ttankbuster/CyberwatchV1B/docs/images/cyan-loading.png

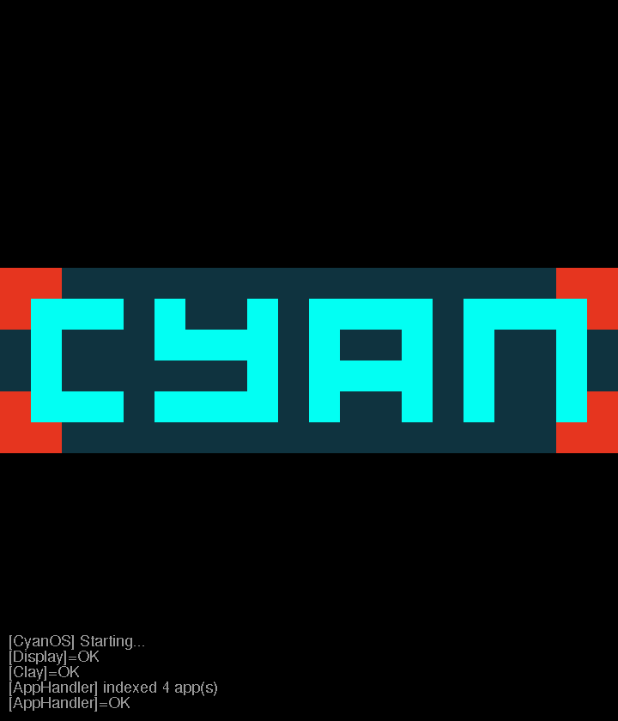
docs/images/cyan-loading.png
