ttankbuster/CyberwatchV1B/docs/images/dial-design-2.png

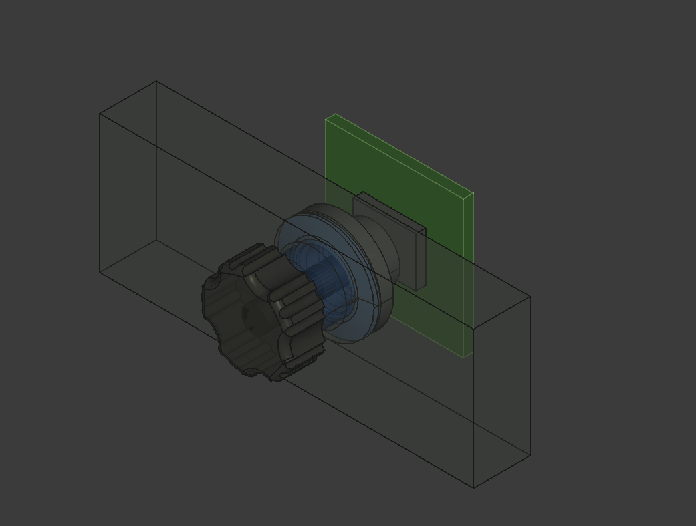
docs/images/dial-design-2.png
