ttankbuster/CyberwatchV1B/docs/images/pcb-3d-2.png

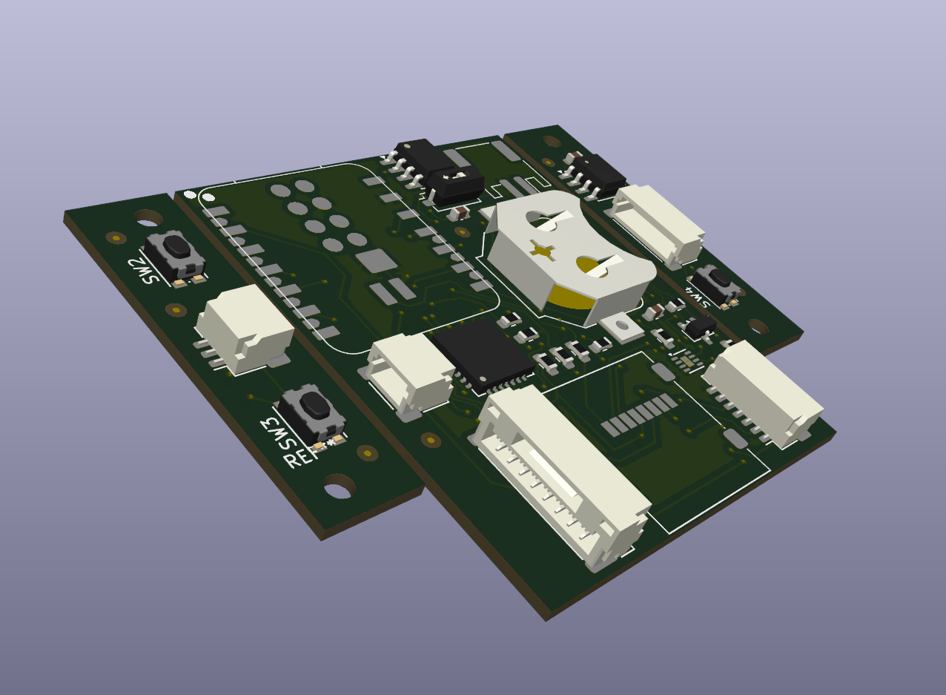
docs/images/pcb-3d-2.png
