ttankbuster/CyberwatchV1B/docs/images/pcb-3d-3.png

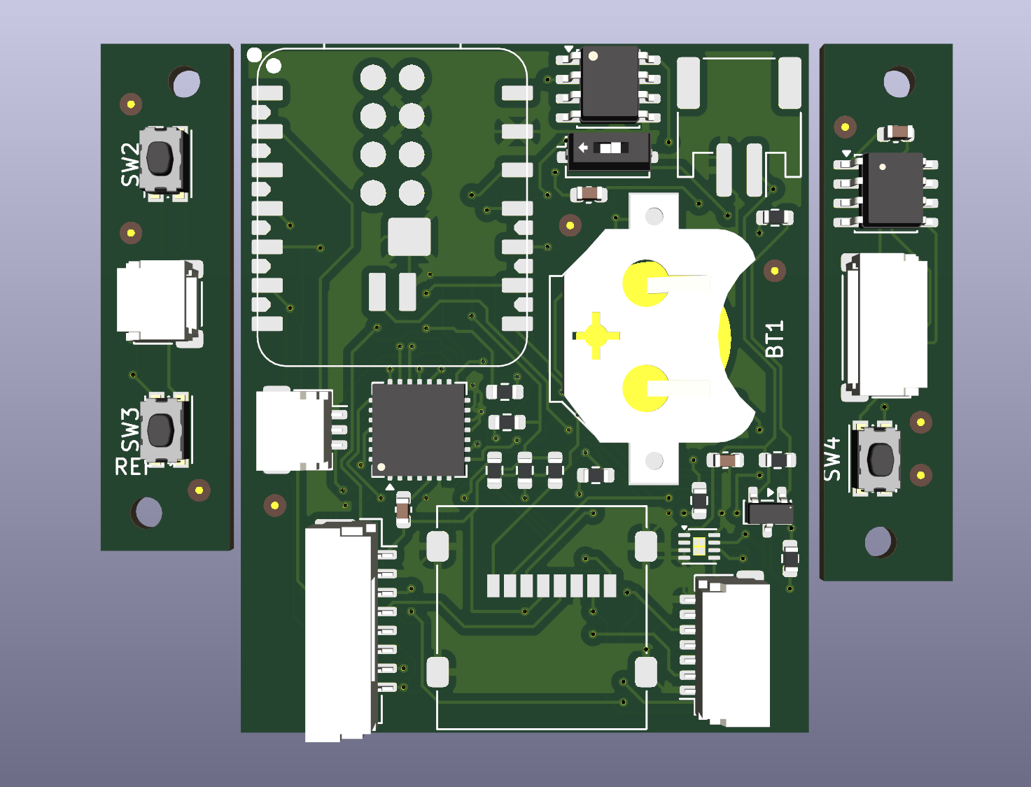
docs/images/pcb-3d-3.png
