ttankbuster/CyberwatchV1B/docs/images/pcb-design.png

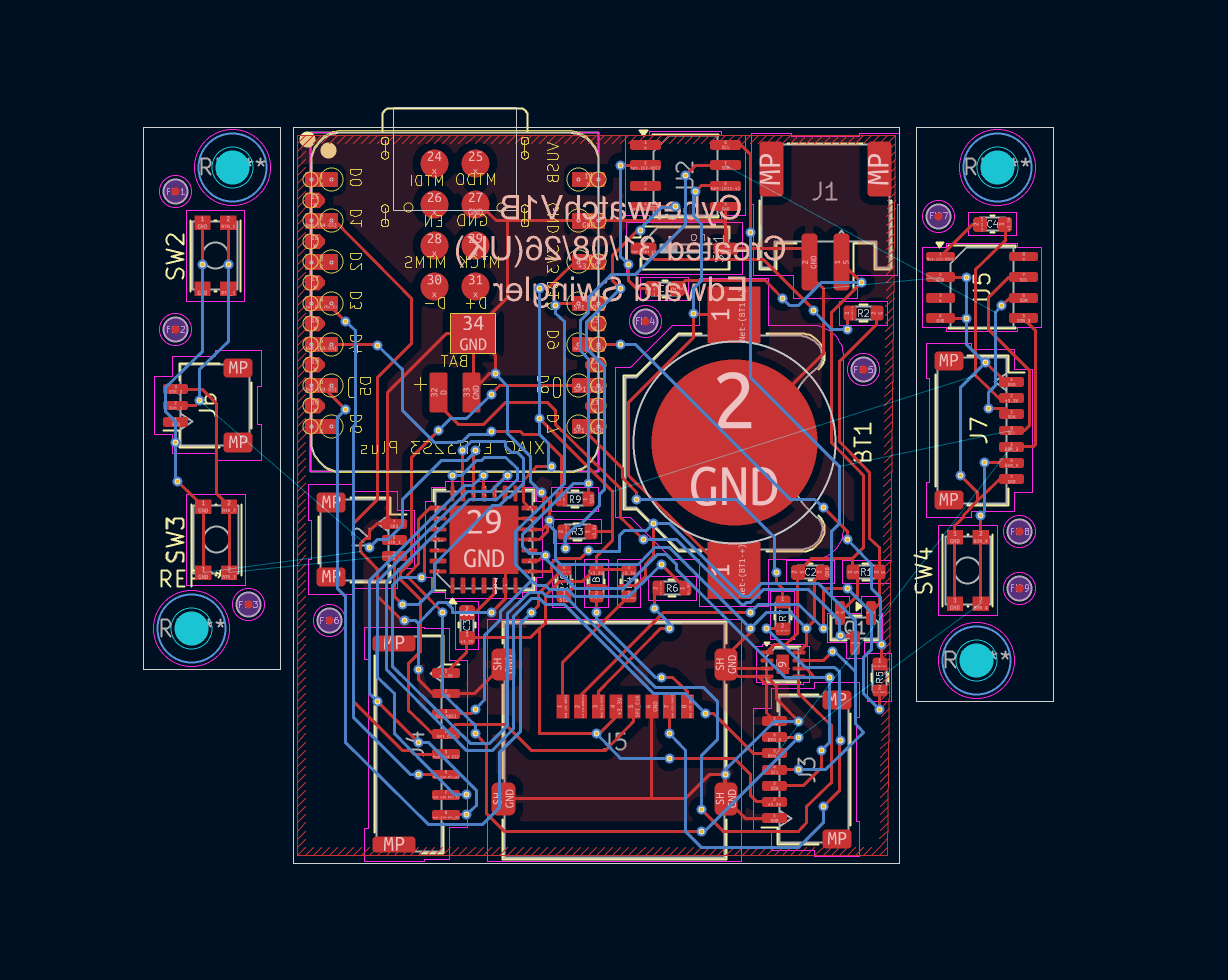
docs/images/pcb-design.png
