ttankbuster/CyberwatchV1B/docs/images/watchface2026-09-0616-29.png

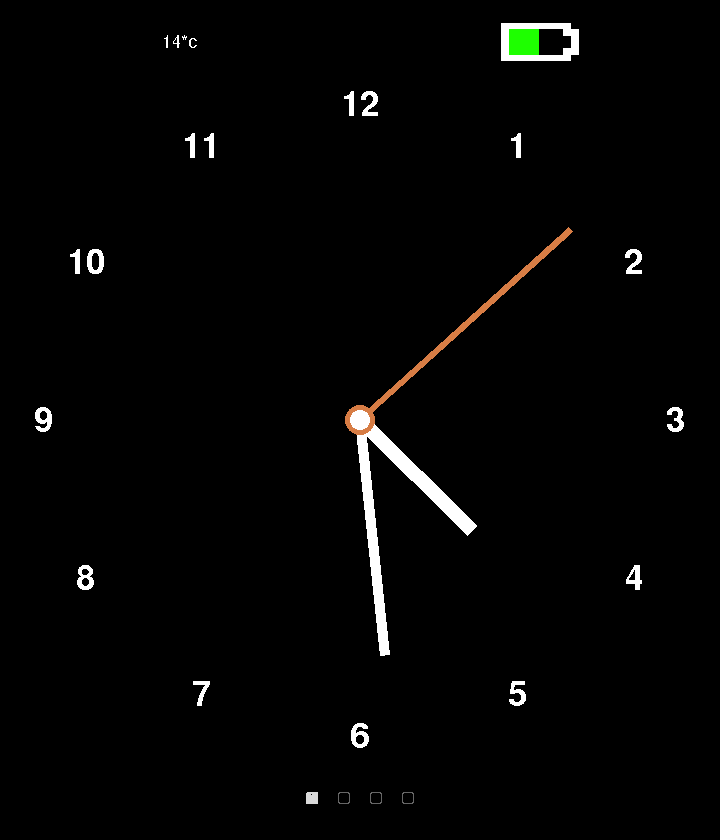
docs/images/watchface2026-09-0616-29.png
