ttankbuster/CyberwatchV1B/docs/images/watchface2026-09-0914-25.png

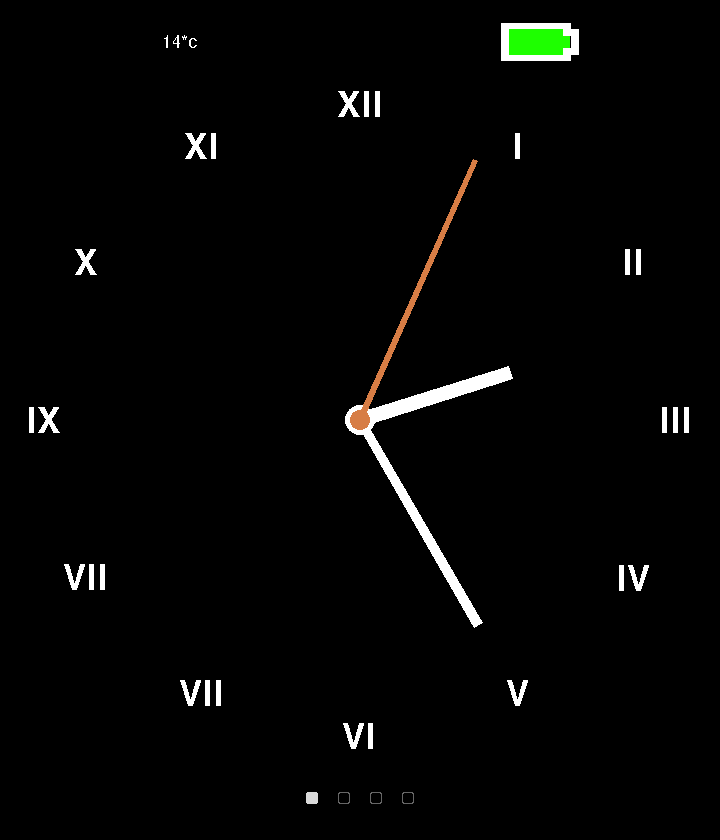
docs/images/watchface2026-09-0914-25.png
