ttankbuster/CyberwatchV1B/docs/images/PCBWayOrderPhotos/T-3P2W1142579A (5).jpg

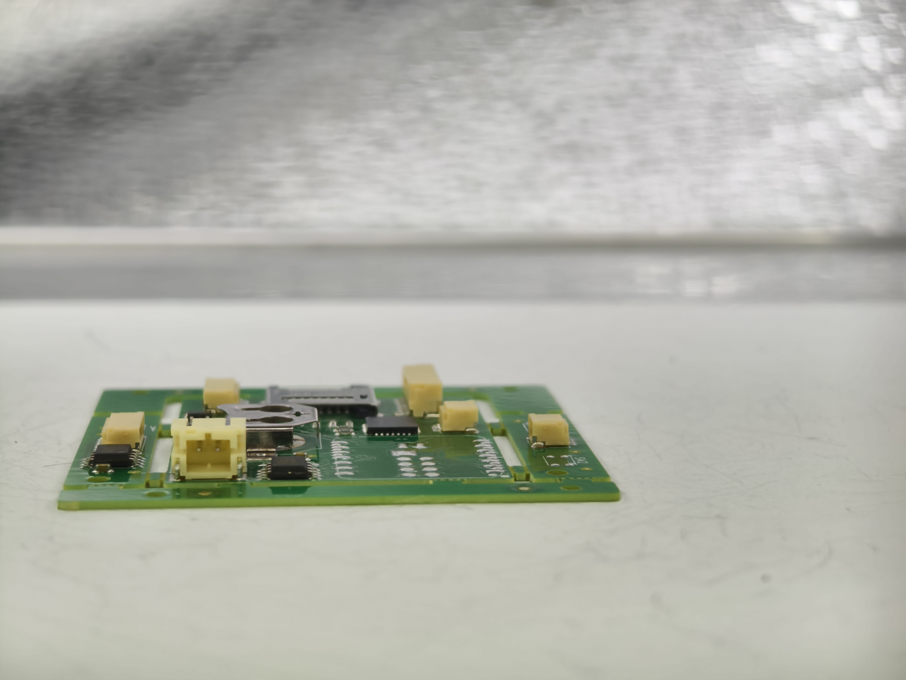
docs/images/PCBWayOrderPhotos/T-3P2W1142579A (5).jpg
