ttankbuster/CyberwatchV1B/cyan/tabs/screen_watchface.c

// screen_watchface.c
#include "../clay_ui.h"
// #include "../data/data.h"
#include "../data/surface.h"
#include <math.h>

#ifndef M_PI
#define M_PI 3.14159265358979323846f
#endif

static void render_time_digital(
    CyanData* data, int debugOpacity, Clay_String timeString, Clay_String dateString, bool mmddyy
) {
    Clay_Sizing expand = {.width = CLAY_SIZING_GROW(0), .height = CLAY_SIZING_GROW(0)};

    CLAY(
        CLAY_ID("Watchface"), {.layout = {.layoutDirection = CLAY_TOP_TO_BOTTOM, .sizing = expand}}
    ) {
        CLAY(
            CLAY_ID("WatchTime"),
            {.backgroundColor = {20, 46, 65, debugOpacity},
             .layout = {
                 .childAlignment = {.x = CLAY_ALIGN_X_CENTER, .y = CLAY_ALIGN_Y_CENTER},
                 .sizing = {.width = CLAY_SIZING_GROW(), .height = CLAY_SIZING_PERCENT(0.6f)}
             }}
        ) {
            CLAY_TEXT(
                timeString, CLAY_TEXT_CONFIG(
                                {.fontId = FONT_LARGE,
                                 .fontSize = 190,
                                 .textColor = data->accentColor}
                            )
            );
        }

        CLAY(
            CLAY_ID("WatchDate"),
            {.backgroundColor = {23, 56, 65, debugOpacity},
             .layout = {
                 .childAlignment = {.x = CLAY_ALIGN_X_CENTER, .y = CLAY_ALIGN_Y_CENTER},
                 .sizing = expand
             }}
        ) {
            CLAY_TEXT(
                dateString, CLAY_TEXT_CONFIG(
                                {.fontId = FONT_INFO, .fontSize = 80, .textColor = SECONDARY_COLOUR}
                            )
            );
        }
    }
}

static const char* ROMAN_NUMERALS[12] = {"I",   "II",   "III", "IV", "V",  "VI",
                                         "VII", "VIII", "IX",  "X",  "XI", "XII"};

static void draw_numerals(
    Surface* surface, int centre_x, int centre_y, float radius, float fontSize, bool show_all,
    bool roman, Clay_Color color
) {
    static const int QUARTER_HOURS[4] = {12, 3, 6, 9};
    int count = show_all ? 12 : 4;

    for (int i = 0; i < count; i++) {
        int hour = show_all ? (i + 1) : QUARTER_HOURS[i];
        float angle = (hour % 12) * (M_PI / 6.0f);
        float direction_x = sinf(angle);
        float direction_y = -cosf(angle);

        char label[4];
        if (roman) {
            snprintf(label, sizeof(label), "%s", ROMAN_NUMERALS[hour - 1]);
        } else {
            snprintf(label, sizeof(label), "%d", hour);
        }

        Clay_TextElementConfig config = {.fontId = FONT_MED, .fontSize = (uint16_t)fontSize};
        Clay_StringSlice slice = {.chars = label, .length = (int32_t)strlen(label)};
        Clay_Dimensions dims = display_measure_text(slice, &config, NULL);

        int x = (int)(centre_x + direction_x * radius - dims.width / 2.0f);
        int y = (int)(centre_y + direction_y * radius - dims.height / 2.0f);

        surface_push_text(surface, x, y, label, FONT_MED, (int)fontSize, color);
    }
}

static void draw_hand(
    Surface* surface, int centre_x, int centre_y, float angle, float length, float thickness,
    Clay_Color color
) {
    float half_thickness = thickness / 2.0f;
    float direction_x = sinf(angle);
    float direction_y = -cosf(angle);
    float perpendicular_x = -direction_y * half_thickness;
    float perpendicular_y = direction_x * half_thickness;

    int x1 = (int)lroundf(centre_x - perpendicular_x);
    int y1 = (int)lroundf(centre_y - perpendicular_y);
    int x2 = (int)lroundf(centre_x + perpendicular_x);
    int y2 = (int)lroundf(centre_y + perpendicular_y);
    int x3 = (int)lroundf(centre_x + direction_x * length + perpendicular_x);
    int y3 = (int)lroundf(centre_y + direction_y * length + perpendicular_y);
    int x4 = (int)lroundf(centre_x + direction_x * length - perpendicular_x);
    int y4 = (int)lroundf(centre_y + direction_y * length - perpendicular_y);

    surface_push_quad(surface, x1, y1, x2, y2, x3, y3, x4, y4, color);
}

static void render_time_analogue(
    CyanData* data, int debugOpacity, float H, float M, float S
) { // [H = hour, M = minute, S = second] measured in radians
    CLAY(
        CLAY_ID("Watchface"),
        {.backgroundColor = {20, 46, 65, debugOpacity},
         .layout = {
             .childAlignment = {.x = CLAY_ALIGN_X_CENTER, .y = CLAY_ALIGN_Y_CENTER},
             .sizing = {.width = CLAY_SIZING_GROW(), .height = CLAY_SIZING_GROW()}
         }}
    ) {
        Surface* surface = &data->watchface.analogueSurface;
        int centre_x = surface->width / 2;
        int centre_y = surface->height / 2;
        float hand_length =
            (surface->width < surface->height ? surface->width : surface->height) / 2.0f - 20.0f;

        draw_numerals(
            surface, centre_x, centre_y, hand_length, hand_length * 0.22f,
            data->watchface.numeralsShowAll, data->watchface.numeralsRoman, INFO_COLOUR
        );

        // Thicknesses and pivot radii as fractions of hand_length, tuned to match the old
        // fixed-pixel look (14px/10px/6px hands, 15px/10px pivot) at the native launch size
        // (hand_length ~316px there) - this way everything stays the same relative size as
        // the face grows/shrinks with the window.
        draw_hand(
            surface, centre_x, centre_y, H, hand_length * 0.5f, hand_length * 0.0443f, INFO_COLOUR
        );
        draw_hand(
            surface, centre_x, centre_y, M, hand_length * 0.75f, hand_length * 0.0316f, INFO_COLOUR
        );
        int pivot_outer_radius = (int)lroundf(hand_length * 0.0475f);
        int pivot_inner_radius = (int)lroundf(hand_length * 0.0316f);
        surface_push_circle(surface, centre_x, centre_y, pivot_outer_radius, INFO_COLOUR);
        surface_push_circle(surface, centre_x, centre_y, pivot_inner_radius, data->accentColor);
        draw_hand(
            surface, centre_x, centre_y, S, hand_length * 0.9f, hand_length * 0.019f,
            data->accentColor
        );
    }
}

void read_time_date(CyanData* data) {
    WatchfaceData* wf = &data->watchface;
    snprintf(wf->timeChars, sizeof(wf->timeChars), "%02d:%02d", wf->time.tm_hour, wf->time.tm_min);

<<<<<<< HEAD
    const char* weekday = WEEKDAYS[wf->time.tm_wday];
    switch (cyan_settings_get()->dateFormat) {
    case DATE_MDY:
        snprintf(
            wf->dateChars, sizeof(wf->dateChars), "%02d/%02d/%02d %.3s", wf->time.tm_mon,
            wf->time.tm_mday, wf->time.tm_year % 100, weekday
        );
        break;
    case DATE_YMD:
        snprintf(
            wf->dateChars, sizeof(wf->dateChars), "%02d/%02d/%02d %.3s", wf->time.tm_year % 100,
            wf->time.tm_mon, wf->time.tm_mday, weekday
        );
        break;
    case DATE_DMY:
    default:
        snprintf(
            wf->dateChars, sizeof(wf->dateChars), "%02d/%02d/%02d %.3s", wf->time.tm_mday,
            wf->time.tm_mon, wf->time.tm_year % 100, weekday
        );
        break;
    }
=======
    int day = wf->time.tm_mday;
    int month = wf->time.tm_mon;
    int year = wf->time.tm_year % 100;
    int first, second, third;
    switch (g_settings.dateFormat) {
    case DATE_MDY:
        first = month;
        second = day;
        third = year;
        break;
    case DATE_YMD:
        first = year;
        second = month;
        third = day;
        break;
    case DATE_DMY:
    default:
        first = day;
        second = month;
        third = year;
        break;
    }
    snprintf(
        wf->dateChars, sizeof(wf->dateChars), "%02d/%02d/%02d %.3s", first, second, third,
        WEEKDAYS[wf->time.tm_wday]
    );
>>>>>>> 46ae89490506ea908522b11788f50b8e0f273993
}

Clay_RenderCommandArray
clay_watchface(CyanData* data, int width, int height, bool analogue, bool show_debug) {
    float deltaTime = get_delta();
    int debugOpacity = show_debug ? 100 : 0;
    read_time_date(data);
    Clay_String timeString = {
        .chars = data->watchface.timeChars,
        .length = strlen(data->watchface.timeChars),
        .isStaticallyAllocated = false
    };
    Clay_String dateString = {
        .chars = data->watchface.dateChars,
        .length = strlen(data->watchface.dateChars),
        .isStaticallyAllocated = false
    };

    int headerHeight = (int)(height * 0.1f);
    int footerHeight = (int)(height * 0.1f);
    Clay_Sizing expand = {.width = CLAY_SIZING_GROW(0), .height = CLAY_SIZING_GROW(0)};

    Clay_SetLayoutDimensions((Clay_Dimensions){(float)width, (float)height});
    Clay_BeginLayout();

    CLAY(
        CLAY_ID("Display"),
        {.layout = {
             .childAlignment = {.x = CLAY_ALIGN_X_CENTER, .y = CLAY_ALIGN_Y_CENTER},
             .layoutDirection = CLAY_TOP_TO_BOTTOM,
             .sizing = expand
         }}
    ) {
        render_header_bar(data, debugOpacity, width, headerHeight);
        if (analogue) {
            surface_init(
                &data->watchface.analogueSurface, 0, headerHeight, width,
                height - headerHeight - footerHeight
            );
            float hourAngle = (data->watchface.time.tm_hour % 12) * (M_PI / 6.0f) +
                              data->watchface.time.tm_min * (M_PI / 360.0f);
            float minuteAngle = data->watchface.time.tm_min * (M_PI / 30.0f);
            float secondAngle = data->watchface.time.tm_sec * (M_PI / 30.0f);
            render_time_analogue(data, debugOpacity, hourAngle, minuteAngle, secondAngle);
        } else {
            render_time_digital(data, debugOpacity, timeString, dateString, false);
        }
        render_footer(data, debugOpacity, footerHeight);
    }

    return Clay_EndLayout(deltaTime);
}
