ttankbuster/CyberwatchV1B/cyan/tabs/screen_app_catalogue.c

//screen_catalogue.c
#include "../clay_ui.h"
#include "../data/data.h"
#include "../app_handling/app_handler.h"



void render_app_handler_catalogue(AppCatalogue *catalogue, AppHandler *app_handler, int width, int height, bool show_debug) {
    int debugOpacity = show_debug ? 255 : 0;

    const int targetCardSize = 100; // rough desired size - actual size is derived below
    int columns = width / targetCardSize;
    if (columns < 1) columns = 1;
    int cardWidth = 70; // guarantees columns * cardWidth == width exactly
    int cardHeight = cardWidth;      // square cards, matching your original .aspectRatio = 1

    int rows = (app_handler->appCount + columns - 1) / columns; // ceil division
    int contentHeight = rows * cardHeight;

    // --- auto-scroll: keep the highlighted card inside the visible viewport ---
    int highlightedRow = catalogue->highlightedApp / columns;
    int cardTop = highlightedRow * cardHeight;
    int cardBottom = cardTop + cardHeight;
    if (cardTop < catalogue->catalogueScrollY) {
        catalogue->catalogueScrollY = cardTop;
    } else if (cardBottom > catalogue->catalogueScrollY + height) {
        catalogue->catalogueScrollY = cardBottom - height;
    }
    if (catalogue->catalogueScrollY < 0) catalogue->catalogueScrollY = 0;
    int maxScroll = catalogue->contentHeight - height;
    if (maxScroll < 0) maxScroll = 0;
    if (catalogue->catalogueScrollY > maxScroll) catalogue->catalogueScrollY = maxScroll;

    CLAY(CLAY_ID("AppHandlerDisplay"), {
        .layout = { .sizing = { .width = CLAY_SIZING_GROW(), .height = CLAY_SIZING_GROW() } }
    }) {
        CLAY(CLAY_ID("AppEntrysViewport"), {
            .backgroundColor = BG_COLOR,
            .layout = { .sizing = { .width = CLAY_SIZING_GROW(), .height = CLAY_SIZING_GROW() } },
            .clip = { .vertical = true, .childOffset = { 0, (float) -catalogue->catalogueScrollY } }
        }) {
            CLAY(CLAY_ID("AppEntrysContent"), {
                .layout = {
                    .layoutDirection = CLAY_TOP_TO_BOTTOM,
                    .sizing = { .width = CLAY_SIZING_GROW() }
                }
            }) {
                for (int row = 0; row < rows; row++) {
                    CLAY(CLAY_IDI("AppRow", row), {
                        .layout = { 
                            .sizing = { .width = CLAY_SIZING_GROW(), .height = CLAY_SIZING_FIXED(cardHeight) },
                            .childGap = 10
                        }
                    }) {
                        for (int col = 0; col < columns; col++) {
                            int i = row * columns + col;
                            if (i >= app_handler->appCount) break;
                            AppEntry *app = &app_handler->apps[i];
                            bool highlighted = (i == catalogue->highlightedApp);

                            CLAY(CLAY_IDI("AppCard", i), {
                                .backgroundColor = highlighted ? (Clay_Color){255,255,255,255} : (Clay_Color){20,20,20,255},
                                .layout = {
                                    .layoutDirection = CLAY_TOP_TO_BOTTOM,
                                    .childAlignment = { .x = CLAY_ALIGN_X_CENTER, .y = CLAY_ALIGN_Y_CENTER },
                                    .sizing = { .width = CLAY_SIZING_FIXED(cardWidth), .height = CLAY_SIZING_FIXED(cardHeight) }
                                }
                            }) {
                                CLAY(CLAY_IDI("AppIcon", i), {
                                    .layout = { .sizing = { .width = CLAY_SIZING_FIXED(50), .height = CLAY_SIZING_FIXED(50) } },
                                    .aspectRatio = 1,
                                    .image = { .imageData = app->iconHandle }
                                }) {};

                                Clay_String appNameString = { .isStaticallyAllocated = false, .length = (int32_t) strlen(app->name), .chars = app->name };
                                CLAY_TEXT(appNameString, CLAY_TEXT_CONFIG({
                                    .fontId = FONT_SMALL,
                                    .fontSize = 20,
                                    .textColor = highlighted ? (Clay_Color){0,0,0,255} : INFO_COLOUR,
                                }));
                            }
                        }
                    }
                }
            }
        }
    }
}

Clay_RenderCommandArray clay_app_handler_catalogue(CyanData* data, AppHandler *app_handler,int width, int height, bool show_debug) {
    float deltaTime = get_delta();
    int debugOpacity = show_debug ? 100 : 0;

    int headerHeight = (int) (height * 0.1f);
    int footerHeight = (int) (height * 0.1f);
    Clay_Sizing expand = { .width = CLAY_SIZING_GROW(0), .height = CLAY_SIZING_GROW(0) };

    Clay_SetLayoutDimensions((Clay_Dimensions) { (float) width, (float) height });
    Clay_BeginLayout();

    CLAY(CLAY_ID("Display"), {
        .layout = {
            .childAlignment = { .x = CLAY_ALIGN_X_CENTER, .y = CLAY_ALIGN_Y_CENTER },
            .layoutDirection = CLAY_TOP_TO_BOTTOM,
            .sizing = expand
        }
    }) {
        render_header_bar(data, debugOpacity, width, headerHeight);
        render_app_handler_catalogue(&data->appCatalogue, app_handler, width, height, show_debug);
        render_footer(data, debugOpacity, footerHeight);
    }

    return Clay_EndLayout(deltaTime);
}

void app_handler_catalogue_move(AppCatalogue *catalogue, AppHandler *app_handler, int delta) {
    if (app_handler->appCount == 0) return;
    catalogue->highlightedApp = (catalogue->highlightedApp - delta + app_handler->appCount) % app_handler->appCount;
}
